Raziz1/PCB_Business_Card/Images/resistnace_altium.png

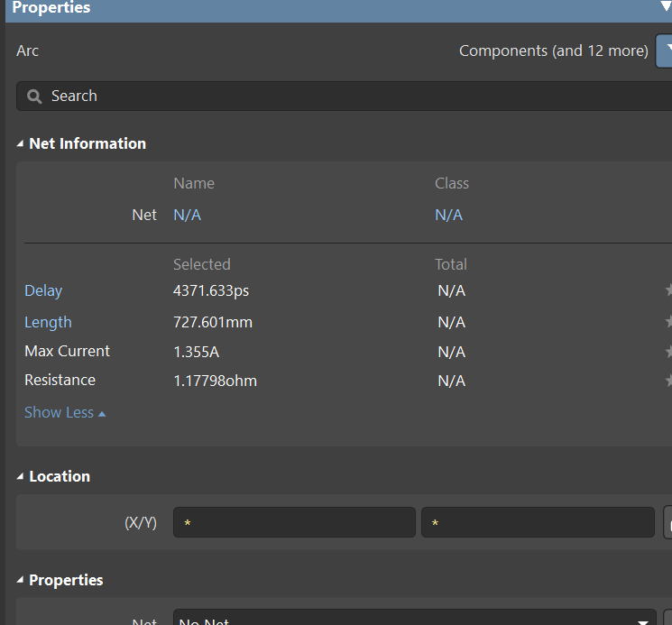
Images/resistnace_altium.png
