Raziz1/PCB_Business_Card/Resource_Documents/AN11276/Class_4/Class_4.jpg

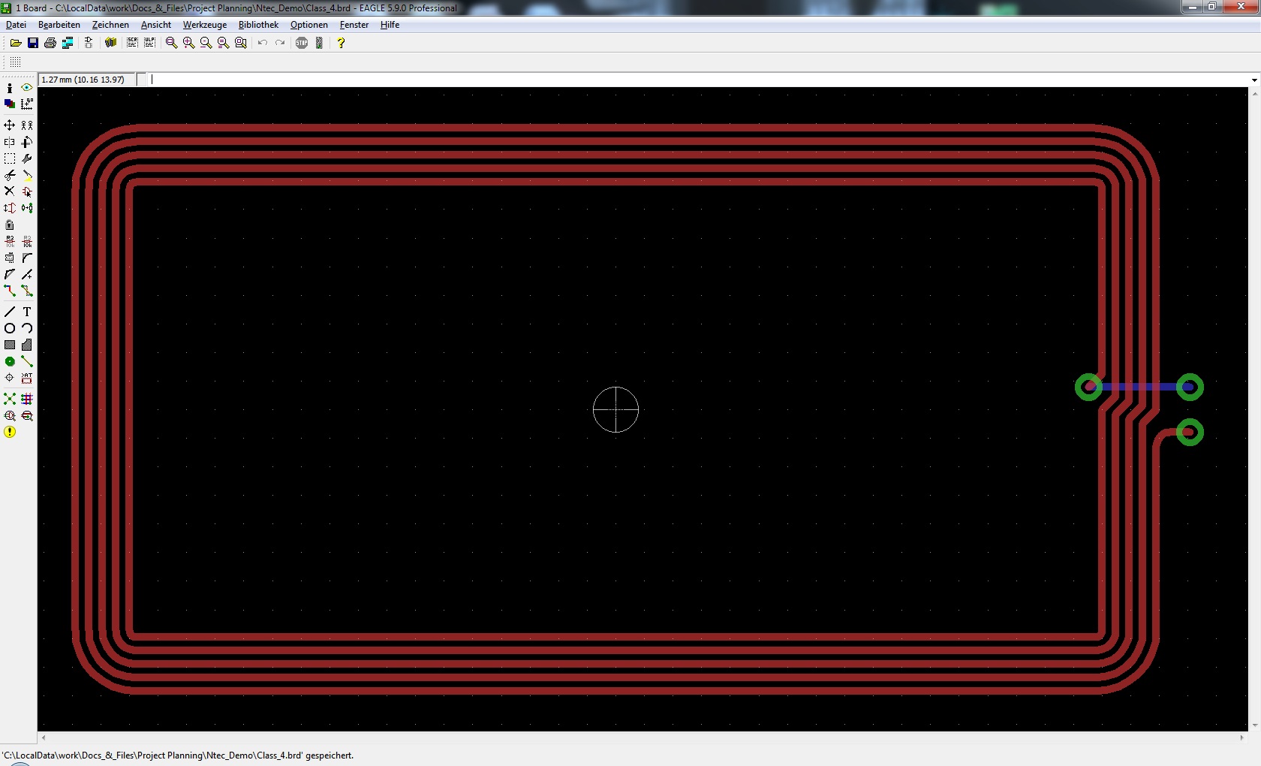
Resource_Documents/AN11276/Class_4/Class_4.jpg
